mekatronik-achmadi/ublik/firmware_1/ublik_conf.h

#ifndef UBLIK_CONF_H
#define UBLIK_CONF_H

#define RUN_TEST 0
#define RUN_WORK 1

#define con_tunda 500
#define ind_tunda 500
#define proc_tunda 500
#define analog_tunda 100

#define SAVER_PERIOD 60  //in second

#define MIN_ADC_LAMP 200
#define MIN_ADC_USB 200

#define LVL_BATT_1 2400
#define LVL_BATT_2 2500
#define LVL_BATT_3 2600
#define LVL_BATT_4 2700

#endif // UBLIK_CONF_H
