mekatronik-achmadi/ublik/firmware_1/sources/ublik.h

#ifndef UBLIK_H
#define UBLIK_H

void ublik_init(void);
void ublik_out(void);
void ublik_ind(void);
void ublik_batt(void);
void ublik_data(void);
void ublik_sleep(void);
void ublik_wkup(void);

#endif // UBLIK_H
