mekatronik-achmadi/ublik/firmware_0/ublik_conf.h

#ifndef UBLIK_CONF_H
#define UBLIK_CONF_H

#define RUN_TEST 1
#define RUN_WORK 0

#define ind_tunda 100
#define con_tunda 100
#define data_tunda 100
#define proc_tunda 100
#define saver_tunda 100
#define analog_tunda 100

#define USE_COMMS 1

#define USE_SAVER 1
#define SAVER_PERIOD 60  //in second

#define MIN_ADC_LAMP 100
#define MIN_ADC_USB 4095

#define LVL_BATT_1 1900
#define LVL_BATT_2 2000
#define LVL_BATT_3 2200
#define LVL_BATT_4 2500

#endif // UBLIK_CONF_H
